elkel53930/etaoin_rinabot2/app/board/exp.py

# _face
#  waan, normal, 
#
# _mouth
#  normal, a, i, u, e, o, t, waan1, waan2
#
# _eyes
#  normal, right, left, bikkuri, kirakira, toji
#  batsu, gyu, mun
#
#
#
#
#
#
#


_EXP = {}
_EXP['face_waan'] =  """
 , , , , , , , , , , , , , , , , , , , ,
 ,1,1, , , , , , , , , , , , , , ,1,1, ,
 , , ,1,1, , , , , , , , , , ,1,1, , , ,
 , , , , ,1, , , , , , , , ,1, , , , , ,
 , , ,1,1, , , , , , , , , , ,1,1, , , ,
 ,1,1, , , , , , , , , , , , , , ,1,1, ,
 , , , , , , , , , , , , , , , , , , , ,
 , ,1, ,1, , , , , , , , , , ,1, ,1, , ,
 ,1, ,1, , , , , , , , , , , , ,1, ,1, ,
 , , , , , ,1,1, , , , ,1,1, , , , , , ,
 , , , , ,1, , ,1,1,1,1, , ,1, , , , , ,
 , , , , ,1, , , , , , , , ,1, , , , , ,
 , , , , ,1, , ,1,1,1,1, , ,1, , , , , ,
 , , , , , ,1,1, , , , ,1,1, , , , , , ,
 , , , , , , , , , , , , , , , , , , , ,
"""



_EXP['face_normal'] = """
 , , , , , , , , , , , , , , , , , , , ,
 , , , , , , , , , , , , , , , , , , , ,
 , , ,1,1, , , , , , , , , , ,1,1, , , ,
 , , ,1,1, , , , , , , , , , ,1,1, , , ,
 , , ,1,1, , , , , , , , , , ,1,1, , , ,
 , , ,1,1, , , , , , , , , , ,1,1, , , ,
 , , , , , , , , , , , , , , , , , , , ,
 , , , , , , , , , , , , , , , , , , , ,
 , , , , , , , , , , , , , , , , , , , ,
 , , , , , , , , , , , , , , , , , , , ,
 , , , , , ,1, , , , , , ,1, , , , , , ,
 , , , , , , ,1,1,1,1,1,1, , , , , , , ,
 , , , , , , , , , , , , , , , , , , , ,
 , , , , , , , , , , , , , , , , , , , ,
 , , , , , , , , , , , , , , , , , , , ,
"""



_EXP['face_3'] = """
 , , , , , , , , , , , , , , , , , , , ,
 , , , , , , , , , , , , , , , , , , , ,
 , ,1,1, , , , , , , , , , , , ,1,1, , ,
 ,1, , ,1, , , , , , , , , , ,1, , ,1, ,
 , , ,1, , , , , , , , , , , , , ,1, , ,
 ,1, , ,1, , , , , , , , , , ,1, , ,1, ,
 , ,1,1, , , , , , , , , , , , ,1,1, , ,
 , , , , , , , , , , , , , , , , , , , ,
 , , , , , , , , , , , , , , , , , , , ,
 , , , , , , , , , , , , , , , , , , , ,
 , , , , , , , , , , , , , , , , , , , ,
 , , , , , , , , , , , , , , , , , , , ,
 , , , , , , , , , , , , , , , , , , , ,
 , , , , , , , , , , , , , , , , , , , ,
 , , , , , , , , , , , , , , , , , , , ,
"""



_EXP['face_2'] = """
 , , , , , , , , , , , , , , , , , , , ,
 , , , , , , , , , , , , , , , , , , , ,
 , ,1,1, , , , , , , , , , , , ,1,1, , ,
 ,1, , ,1, , , , , , , , , , ,1, , ,1, ,
 , , ,1, , , , , , , , , , , , , ,1, , ,
 , ,1, , , , , , , , , , , , , ,1, , , ,
 ,1,1,1,1, , , , , , , , , , ,1,1,1,1, ,
 , , , , , , , , , , , , , , , , , , , ,
 , , , , , , , , , , , , , , , , , , , ,
 , , , , , , , , , , , , , , , , , , , ,
 , , , , , , , , , , , , , , , , , , , ,
 , , , , , , , , , , , , , , , , , , , ,
 , , , , , , , , , , , , , , , , , , , ,
 , , , , , , , , , , , , , , , , , , , ,
 , , , , , , , , , , , , , , , , , , , ,
"""



_EXP['face_1'] = """
 , , , , , , , , , , , , , , , , , , , ,
 , , , , , , , , , , , , , , , , , , , ,
 , , ,1, , , , , , , , , , , , , ,1, , ,
 , ,1,1, , , , , , , , , , , , ,1,1, , ,
 , , ,1, , , , , , , , , , , , , ,1, , ,
 , , ,1, , , , , , , , , , , , , ,1, , ,
 , ,1,1,1, , , , , , , , , , , ,1,1,1, ,
 , , , , , , , , , , , , , , , , , , , ,
 , , , , , , , , , , , , , , , , , , , ,
 , , , , , , , , , , , , , , , , , , , ,
 , , , , , , , , , , , , , , , , , , , ,
 , , , , , , , , , , , , , , , , , , , ,
 , , , , , , , , , , , , , , , , , , , ,
 , , , , , , , , , , , , , , , , , , , ,
 , , , , , , , , , , , , , , , , , , , ,
"""



_EXP['face_non'] =  """
 , , , , , , , , , , , , , , , , , , , ,
 , , , , , , , , , , , , , , , , , , , ,
 , , , , , , , , , , , , , , , , , , , ,
 , , , , , , , , , , , , , , , , , , , ,
 , , , , , , , , , , , , , , , , , , , ,
 , , , , , , , , , , , , , , , , , , , ,
 , , , , , , , , , , , , , , , , , , , ,
 , , , , , , , , , , , , , , , , , , , ,
 , , , , , , , , , , , , , , , , , , , ,
 , , , , , , , , , , , , , , , , , , , ,
 , , , , , , , , , , , , , , , , , , , ,
 , , , , , , , , , , , , , , , , , , , ,
 , , , , , , , , , , , , , , , , , , , ,
 , , , , , , , , , , , , , , , , , , , ,
 , , , , , , , , , , , , , , , , , , , ,
"""



_EXP['face_nikkori'] =  """
 , , , , , , , , , , , , , , , , , , , ,
 ,1,1, , , , , , , , , , , , , , ,1,1, ,
 , , ,1,1, , , , , , , , , , ,1,1, , , ,
 , , , , ,1, , , , , , , , ,1, , , , , ,
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
 , , , , , , , , , , , , , , , , , , , ,
 , , , , , , , , , , , , , , , , , , , ,
 , , , , , , , , , , , , , , , , , , , ,
 , , , , , , , , , , , , , , , , , , , ,
 , , , , , , , , , , , , , , , , , , , ,
 , , , , , , , , , , , , , , , , , , , ,
 , , , , , , , , , , , , , , , , , , , ,
"""
